svirant/gSerialEnabler/images/1.JPG

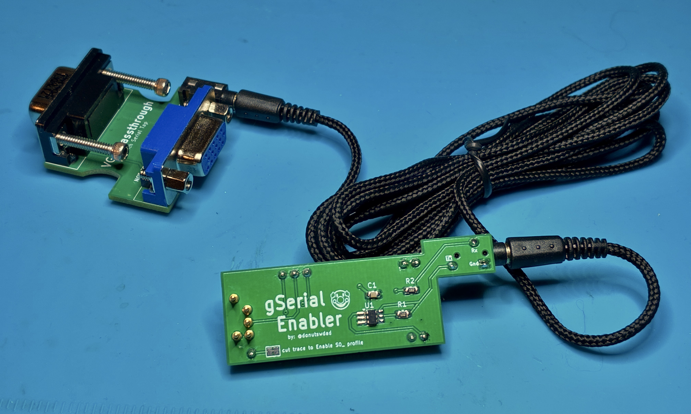
images/1.JPG
